kedube/o2-analyzer/include/FreeSans9pt7bSubset.h

/*****************************************************************************
* 
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
*****************************************************************************/

#pragma once
#include <Adafruit_GFX.h>

const uint8_t FreeSans9pt7bSubsetBitmaps[] PROGMEM = {
    0xFF, 0xFF, 0xF8, 0xC0, 0xC0, 0x08, 0x44, 0x21, 0x10, 0x84, 0x42, 0x11,
    0x08, 0x00, 0x3C, 0x66, 0x42, 0xC3, 0xC3, 0xC3, 0xC3, 0xC3, 0xC3, 0xC3,
    0x42, 0x66, 0x3C, 0x11, 0x3F, 0x33, 0x33, 0x33, 0x33, 0x30, 0x3E, 0x31,
    0xB0, 0x78, 0x30, 0x18, 0x1C, 0x1C, 0x1C, 0x18, 0x18, 0x10, 0x08, 0x07,
    0xF8, 0x3C, 0x66, 0xC3, 0xC3, 0x03, 0x06, 0x1C, 0x07, 0x03, 0xC3, 0xC3,
    0x66, 0x3C, 0x0C, 0x18, 0x71, 0x62, 0xC9, 0xA3, 0x46, 0xFE, 0x18, 0x30,
    0x60, 0xC0, 0x7F, 0x20, 0x10, 0x08, 0x08, 0x07, 0xF3, 0x8C, 0x03, 0x01,
    0x80, 0xF0, 0x6C, 0x63, 0xE0, 0x1E, 0x31, 0x98, 0x78, 0x0C, 0x06, 0xF3,
    0x8D, 0x83, 0xC1, 0xE0, 0xD0, 0x6C, 0x63, 0xE0, 0xFF, 0x03, 0x02, 0x06,
    0x04, 0x0C, 0x08, 0x18, 0x18, 0x18, 0x10, 0x30, 0x30, 0x3E, 0x31, 0xB0,
    0x78, 0x3C, 0x1B, 0x18, 0xF8, 0xC6, 0xC1, 0xE0, 0xF0, 0x6C, 0x63, 0xE0,
    0x3C, 0x66, 0xC2, 0xC3, 0xC3, 0xC3, 0x67, 0x3B, 0x03, 0x03, 0xC2, 0x66,
    0x3C, 0xC0, 0x00, 0x30, 0x06, 0x00, 0xF0, 0x0F, 0x00, 0x90, 0x19, 0x81,
    0x98, 0x10, 0x83, 0x0C, 0x3F, 0xC2, 0x04, 0x60, 0x66, 0x06, 0xC0, 0x30,
    0xFF, 0x18, 0x33, 0x03, 0x60, 0x6C, 0x0D, 0x83, 0x3F, 0xC6, 0x06, 0xC0,
    0x78, 0x0F, 0x01, 0xE0, 0x6F, 0xF8, 0x1F, 0x86, 0x19, 0x81, 0xA0, 0x3C,
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
    {222, 9, 13, 11, 1, -12}, // 0x45 'E'
    {515, 8, 13, 11, 1, -12}, // 0x46 'F'
    {0, 0, 0, 14, 0, 0}, // 0x47 'G'
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
};

const GFXfont FreeSans9pt7bSubset PROGMEM = {
    (uint8_t *)FreeSans9pt7bSubsetBitmaps,
    (GFXglyph *)FreeSans9pt7bSubsetGlyphs,
    0x20,
    0x7A,
    22
};
