kedube/o2-analyzer/include/FreeSansBold18pt7bSubset.h

/*****************************************************************************
* 
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
*****************************************************************************/

#pragma once
#include <Adafruit_GFX.h>

const uint8_t FreeSansBold18pt7bSubsetBitmaps[] PROGMEM = {
    0x0F, 0x00, 0x1C, 0x01, 0xFE, 0x00, 0xE0, 0x1F, 0xF8, 0x0E, 0x00, 0xFF,
    0xC0, 0x70, 0x0F, 0x0F, 0x07, 0x00, 0x70, 0x38, 0x38, 0x03, 0x81, 0xC3,
    0x80, 0x1C, 0x0E, 0x3C, 0x00, 0xF0, 0xF1, 0xC0, 0x03, 0xFF, 0x1C, 0x00,
    0x1F, 0xF8, 0xE0, 0x00, 0x7F, 0x8E, 0x00, 0x00, 0xF0, 0x70, 0xF8, 0x00,
    0x07, 0x1F, 0xF0, 0x00, 0x39, 0xFF, 0xC0, 0x03, 0x8F, 0xFE, 0x00, 0x1C,
    0xF0, 0x78, 0x01, 0xC7, 0x01, 0xC0, 0x0C, 0x38, 0x0E, 0x00, 0xE1, 0xC0,
    0x70, 0x06, 0x0F, 0x07, 0x80, 0x70, 0x3F, 0xF8, 0x07, 0x01, 0xFF, 0xC0,
    0x38, 0x07, 0xFC, 0x03, 0x80, 0x0F, 0x80, 0xFF, 0xFF, 0xFF, 0x80, 0x07,
    0xF0, 0x0F, 0xFE, 0x0F, 0xFF, 0x87, 0xFF, 0xC7, 0xE3, 0xF3, 0xE0, 0xF9,
    0xF0, 0x7D, 0xF0, 0x1F, 0xF8, 0x0F, 0xFC, 0x07, 0xFE, 0x03, 0xFF, 0x01,
    0xFF, 0x80, 0xFF, 0xC0, 0x7F, 0xE0, 0x3F, 0xF0, 0x1F, 0xF8, 0x0F, 0xFC,
    0x07, 0xDF, 0x07, 0xCF, 0x83, 0xE7, 0xE3, 0xF1, 0xFF, 0xF0, 0xFF, 0xF8,
    0x3F, 0xF8, 0x07, 0xF0, 0x00, 0x01, 0xC0, 0xF0, 0x3C, 0x1F, 0x1F, 0xFF,
    0xFF, 0xFF, 0xFF, 0x07, 0xC1, 0xF0, 0x7C, 0x1F, 0x07, 0xC1, 0xF0, 0x7C,
    0x1F, 0x07, 0xC1, 0xF0, 0x7C, 0x1F, 0x07, 0xC1, 0xF0, 0x7C, 0x1F, 0x07,
    0xC0, 0x07, 0xF0, 0x0F, 0xFE, 0x0F, 0xFF, 0x8F, 0xFF, 0xE7, 0xE3, 0xF7,
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
    {0, 0, 0, 23, 0, 0}, // 0x45 'E'
    {0, 0, 0, 22, 0, 0}, // 0x46 'F'
    {0, 0, 0, 27, 0, 0}, // 0x47 'G'
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
};

const GFXfont FreeSansBold18pt7bSubset PROGMEM = {
    (uint8_t *)FreeSansBold18pt7bSubsetBitmaps,
    (GFXglyph *)FreeSansBold18pt7bSubsetGlyphs,
    0x20,
    0x7E,
    42
};
